Bread80/Datapoint2200/Decoder/Decoder.png

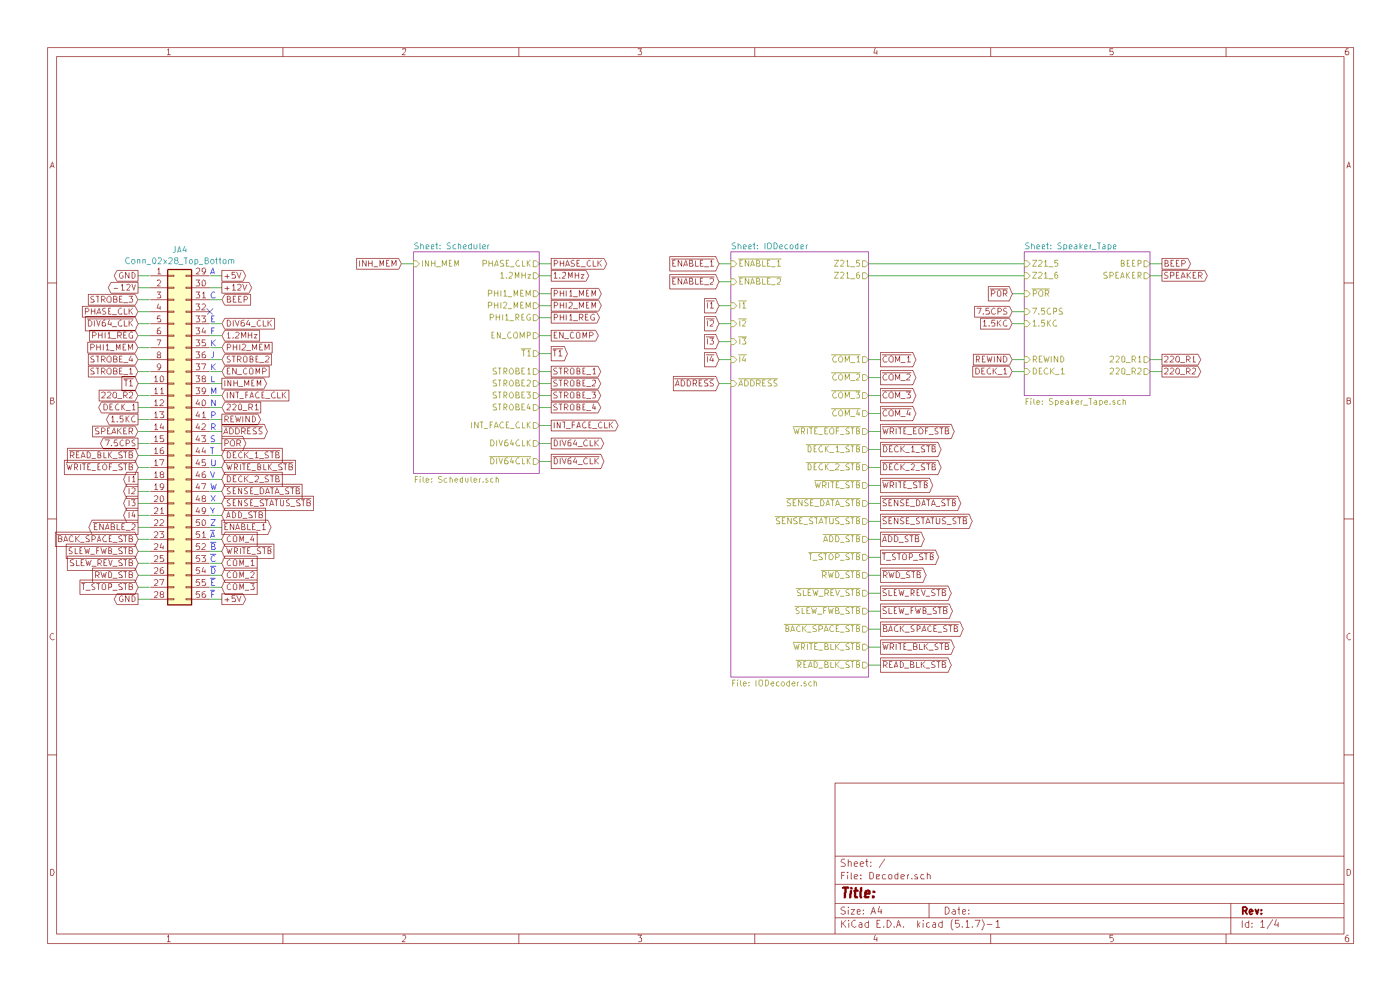
Decoder/Decoder.png
