Bread80/Datapoint2200/Decoder/IODecoder.png

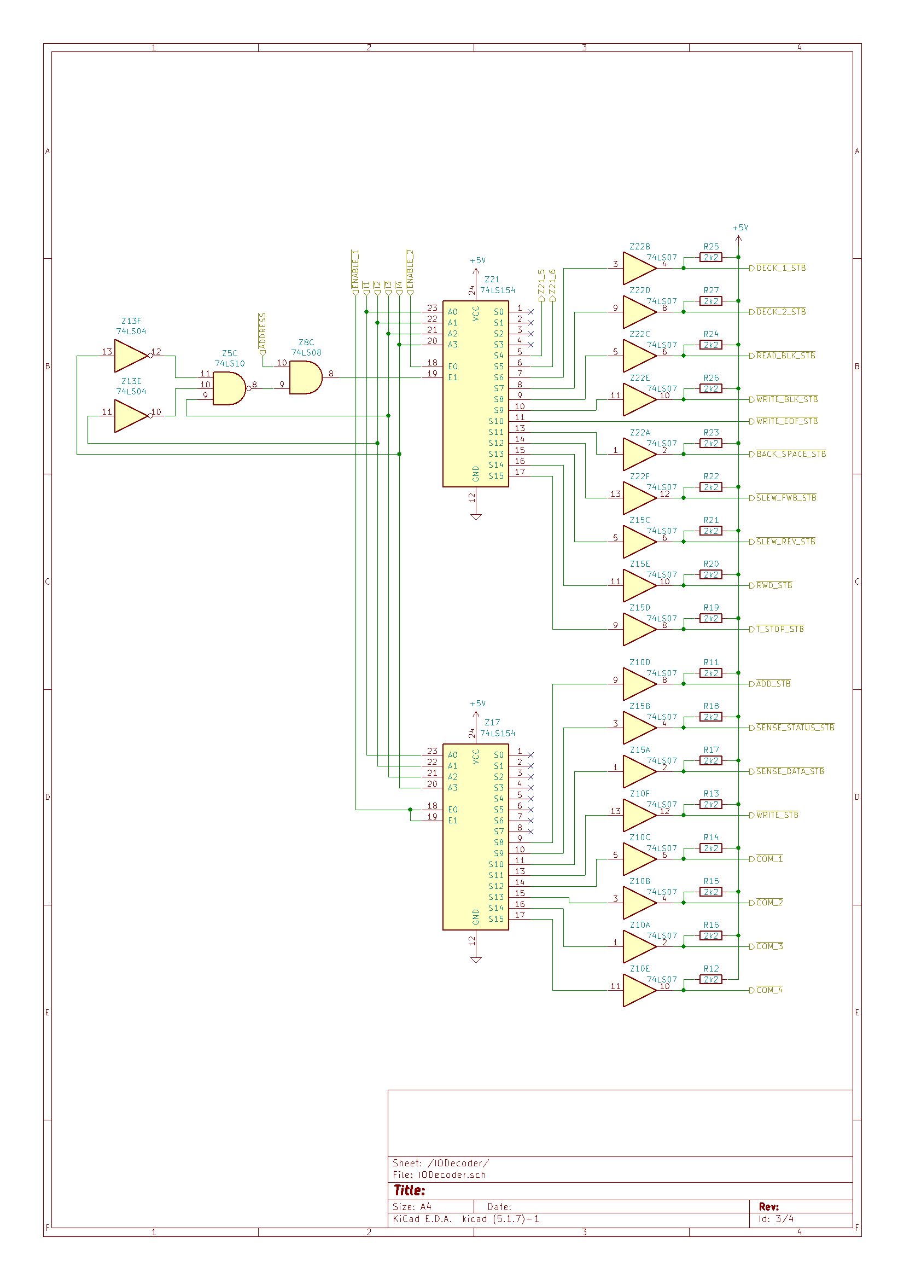
Decoder/IODecoder.png
