Bread80/Datapoint2200/Decoder/Scheduler.png

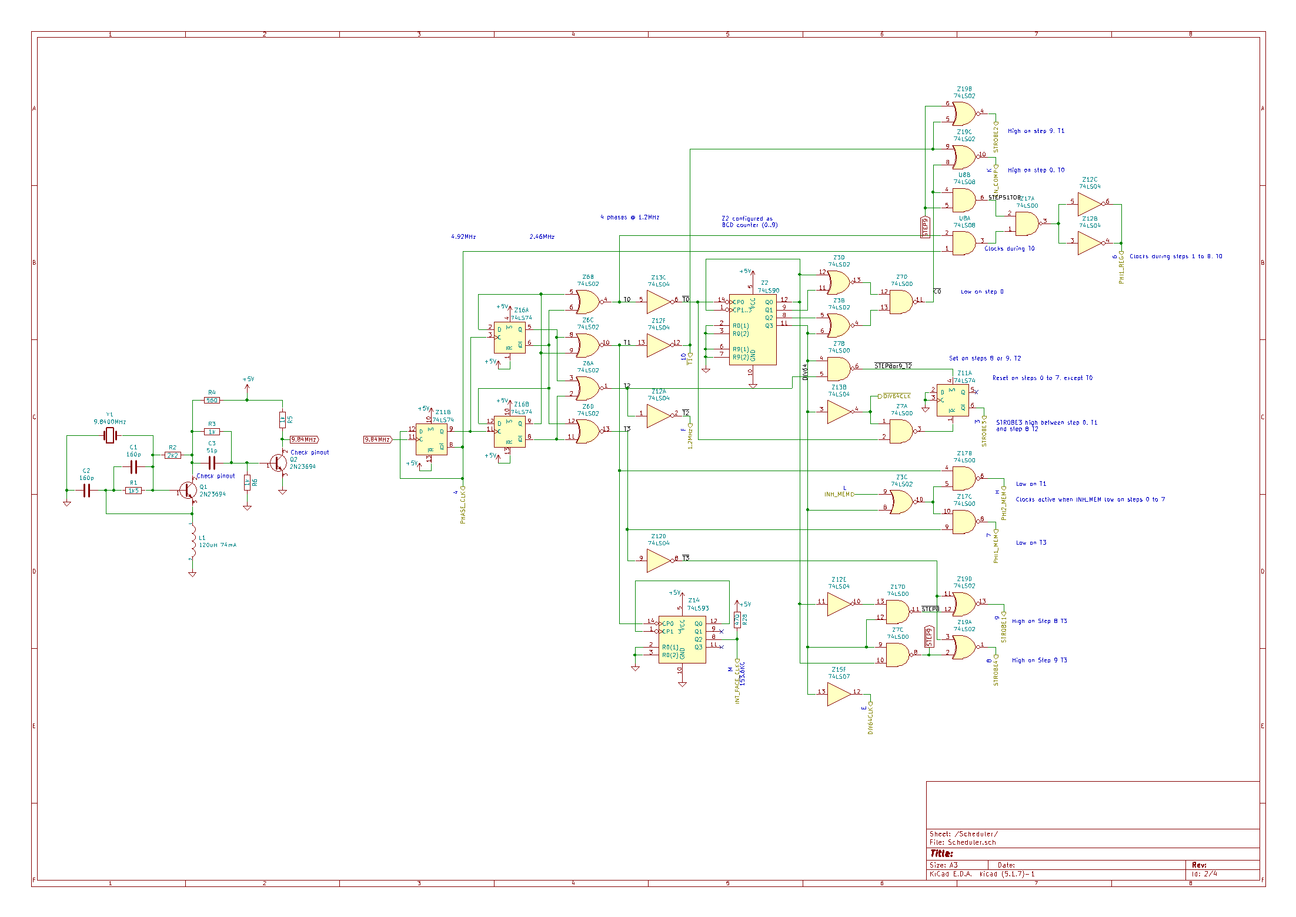
Decoder/Scheduler.png
