Bread80/Datapoint2200/Decoder/Speaker_Tape.png

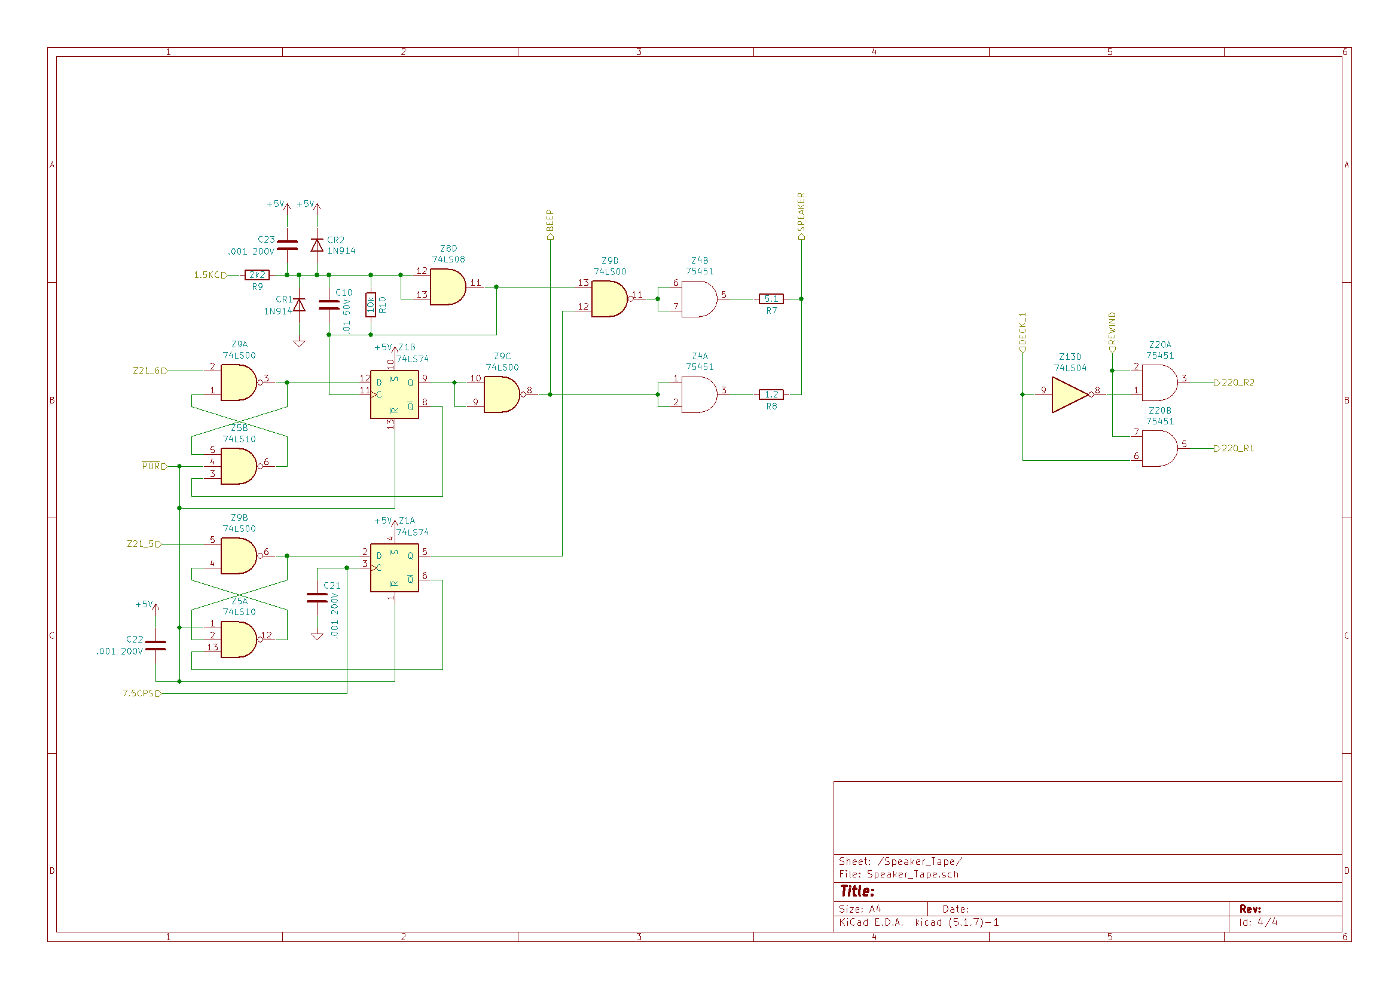
Decoder/Speaker_Tape.png
