Bread80/Datapoint2200/Processor/AddressReg.png

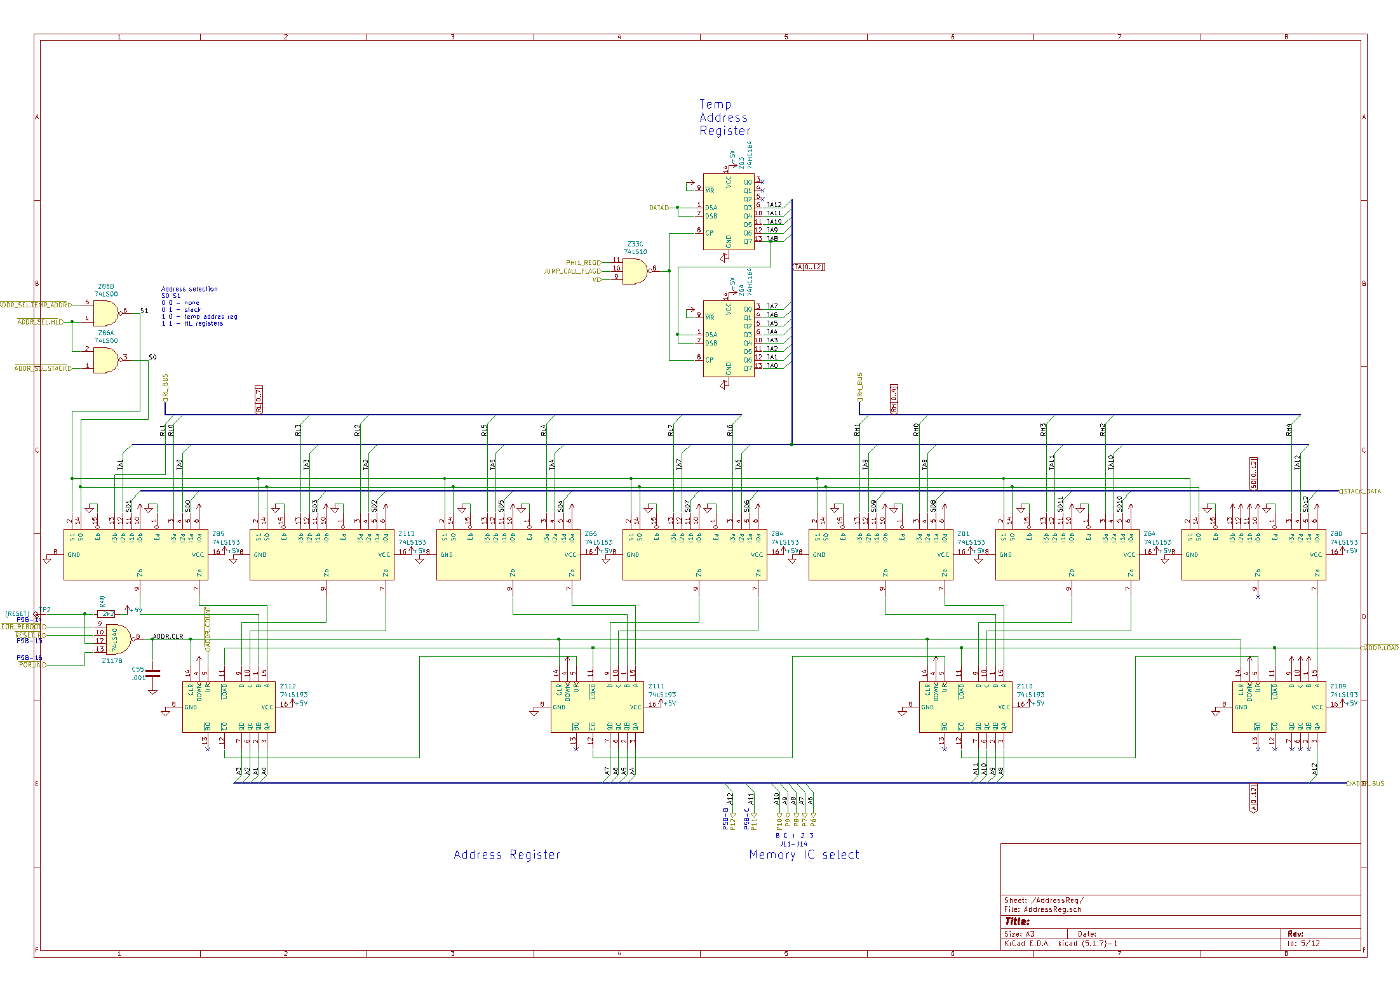
Processor/AddressReg.png
