Bread80/Datapoint2200/Processor/AddrRegAndStackControl.png

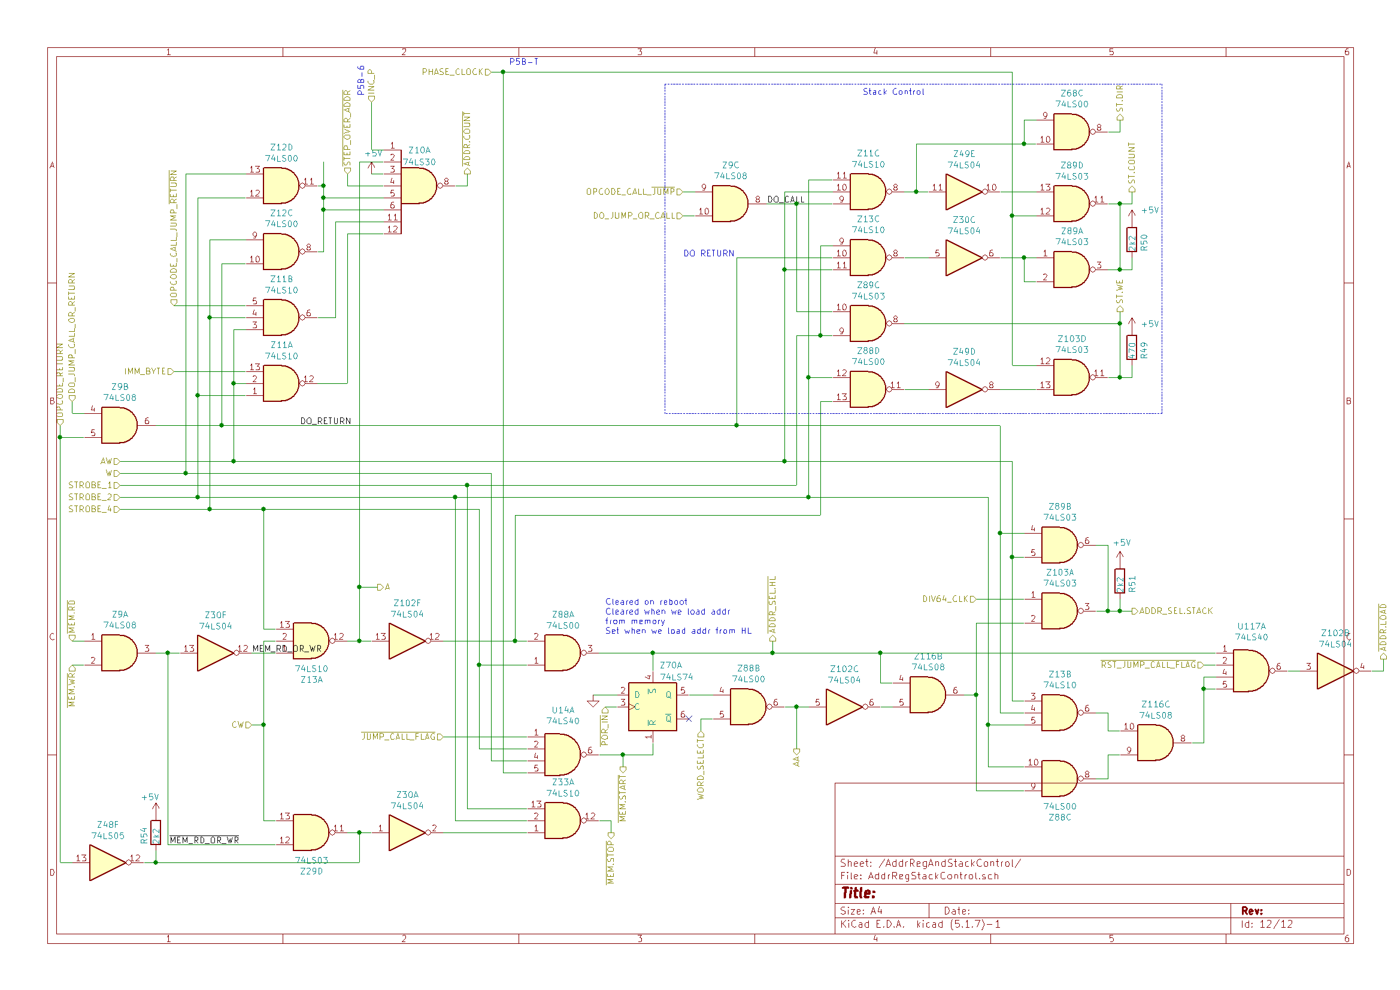
Processor/AddrRegAndStackControl.png
