Bread80/Datapoint2200/Processor/ARegister.png

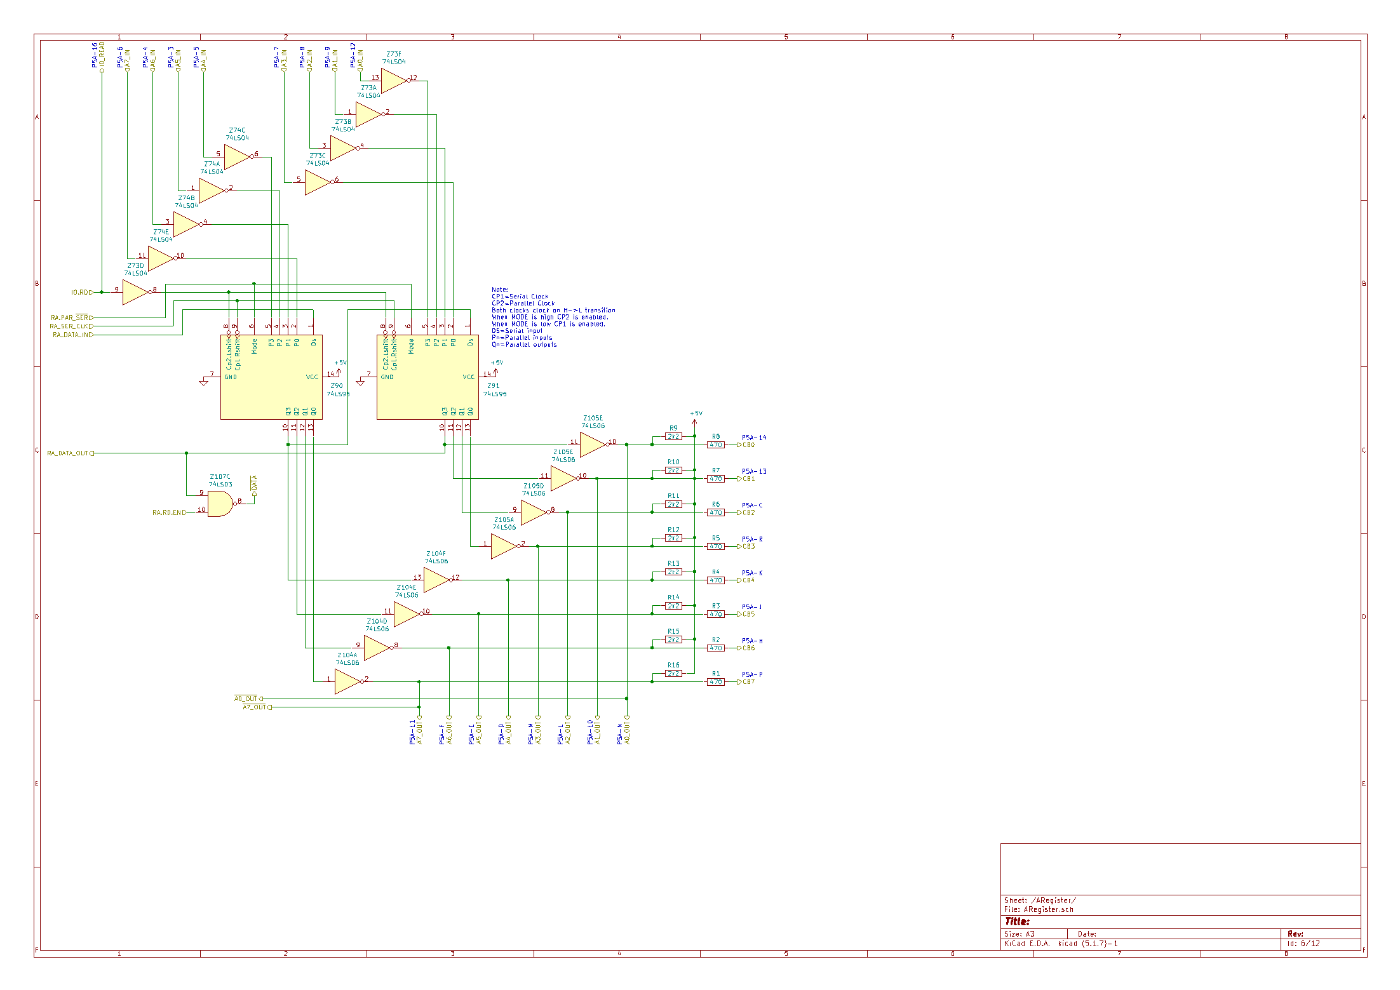
Processor/ARegister.png
