Bread80/Datapoint2200/Processor/Flags.png

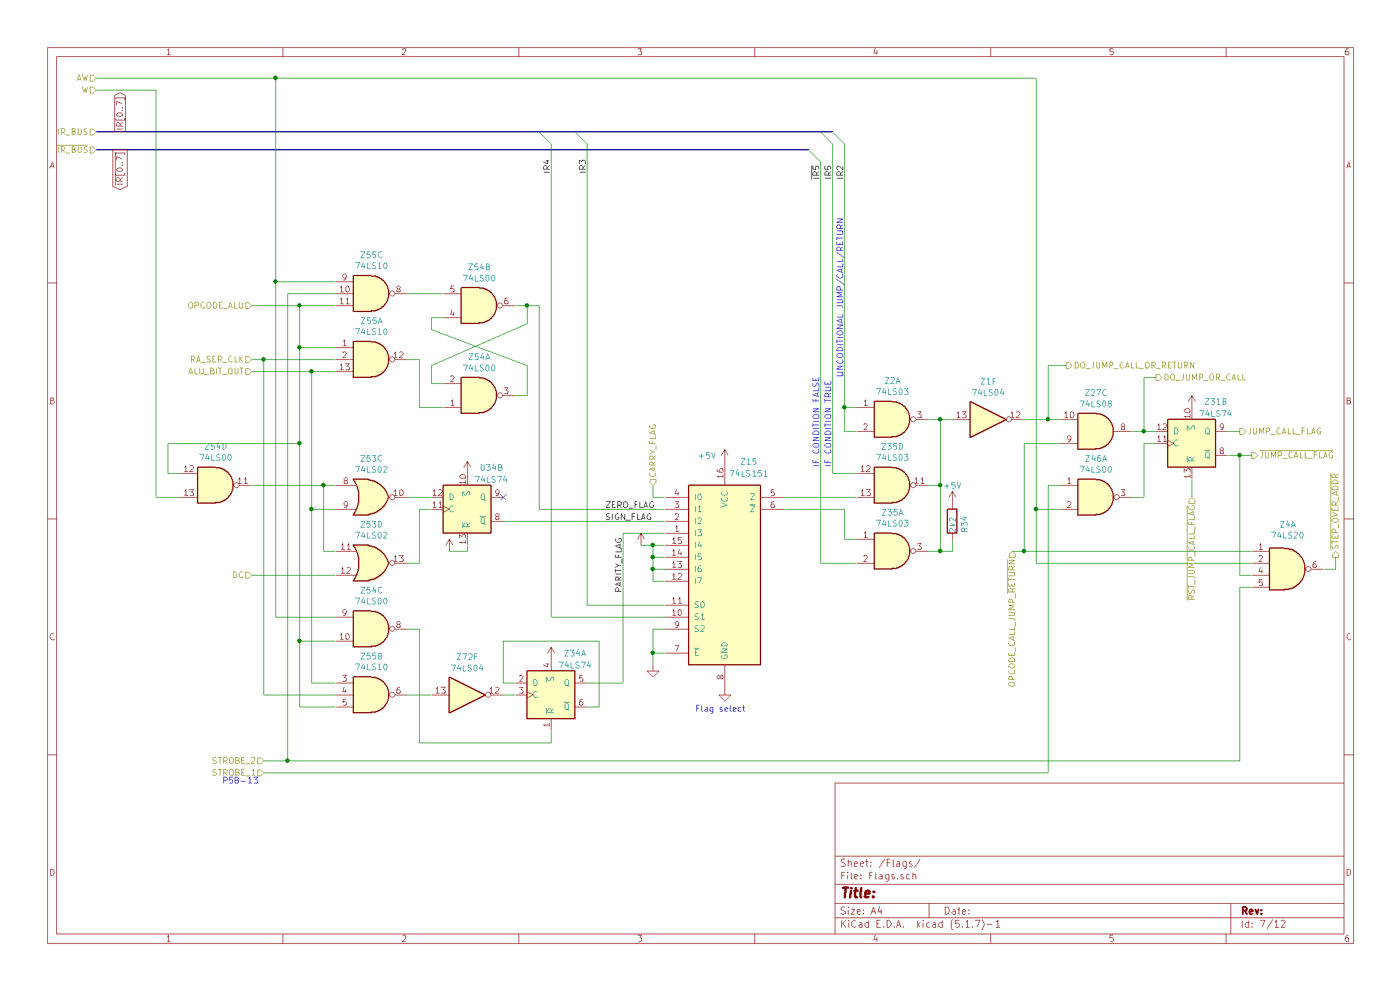
Processor/Flags.png
