Bread80/Datapoint2200/Processor/InstrDecoding.png

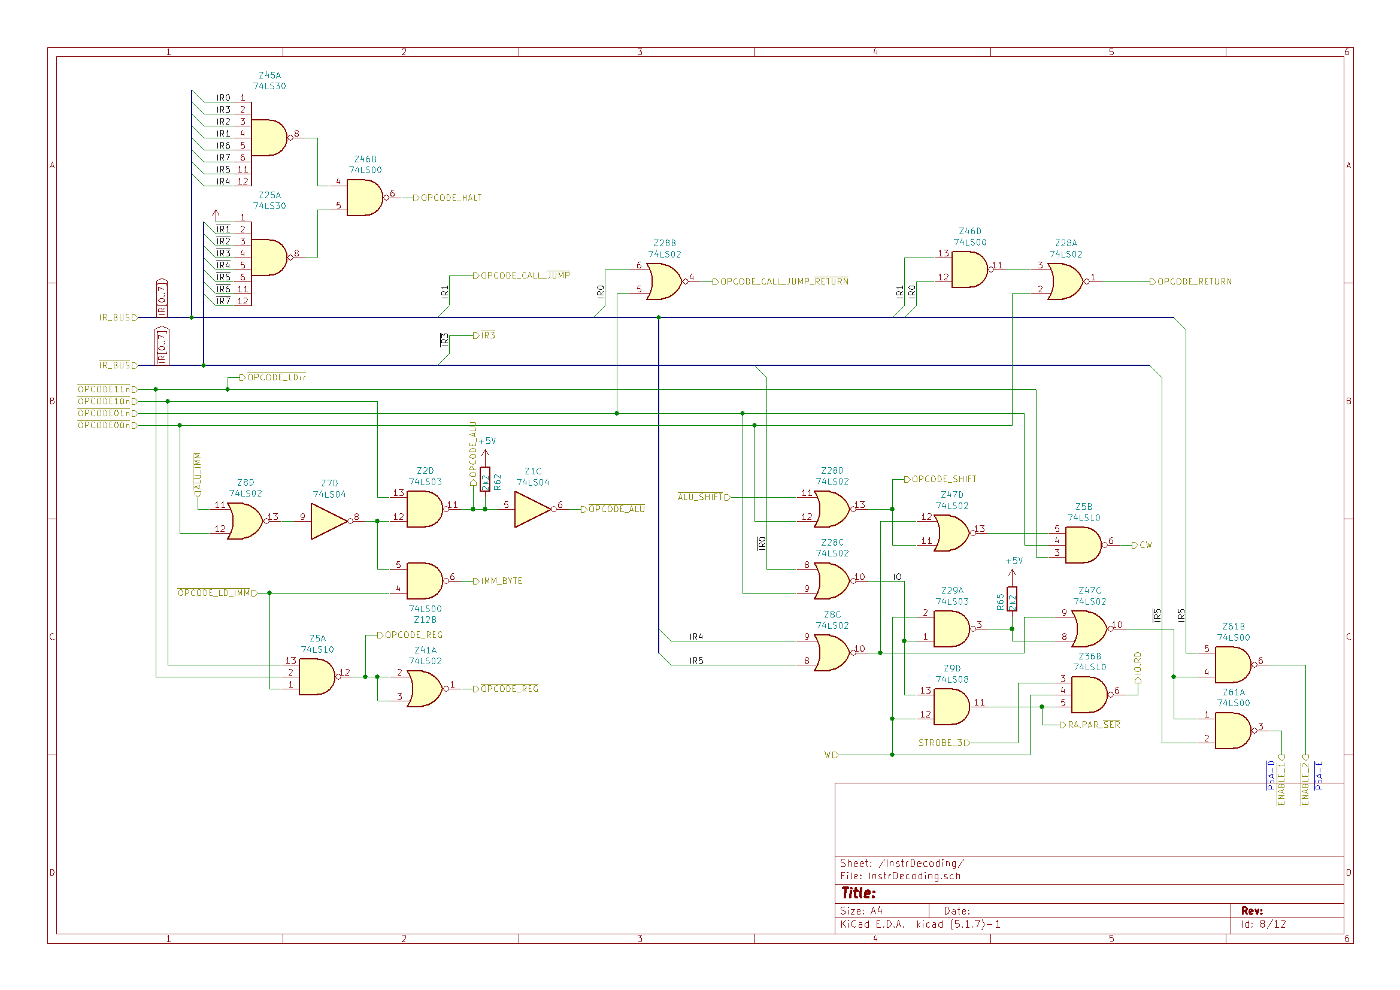
Processor/InstrDecoding.png
