Bread80/Datapoint2200/Processor/IRegister.png

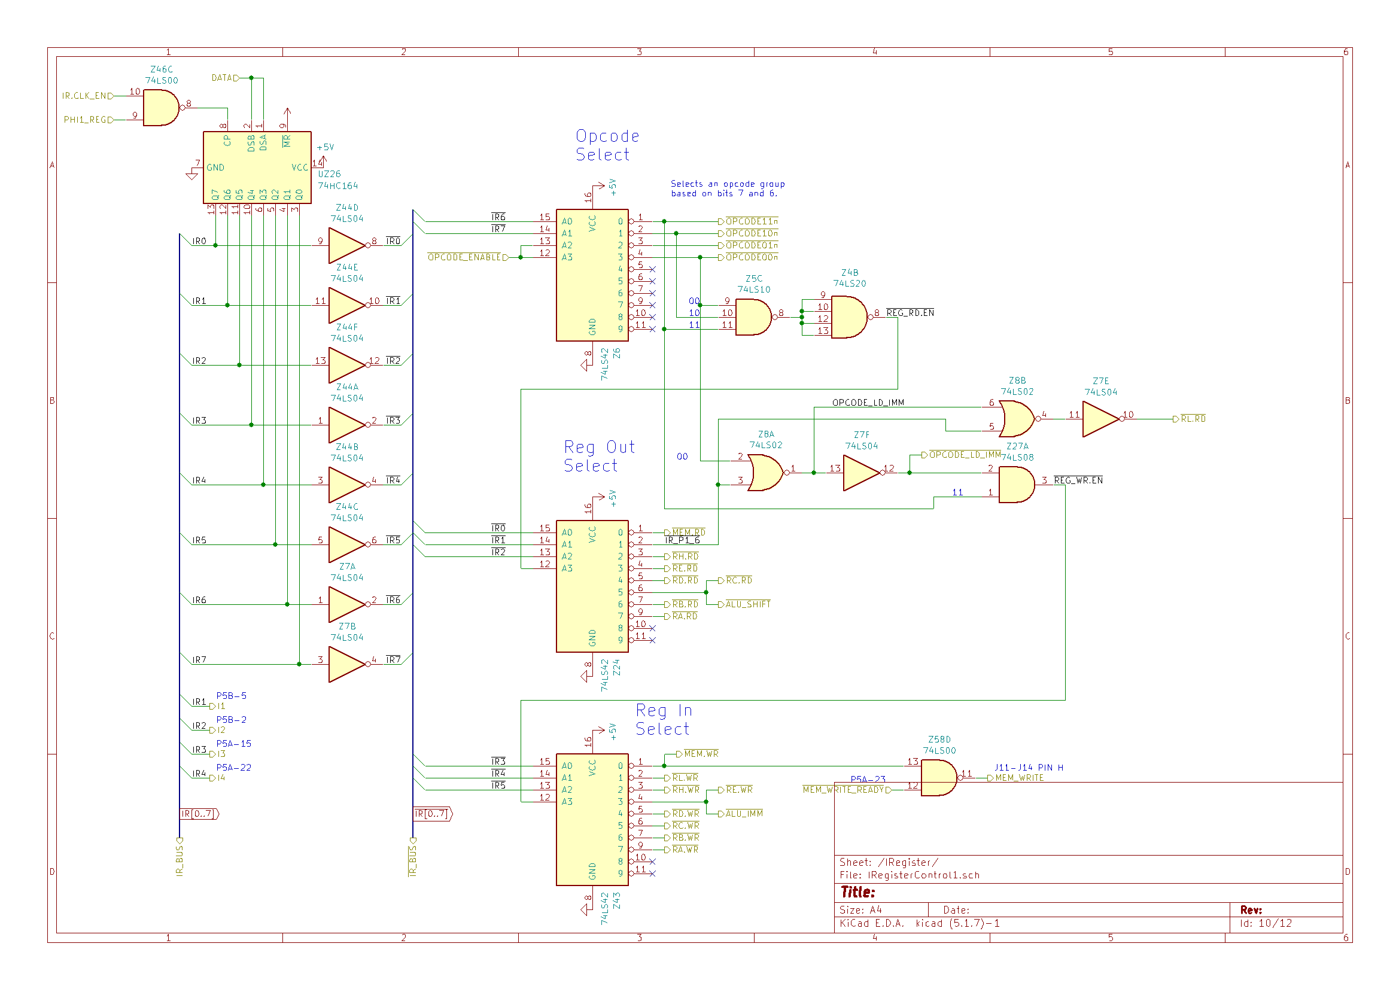
Processor/IRegister.png
