Bread80/Datapoint2200/Processor/Processor.png

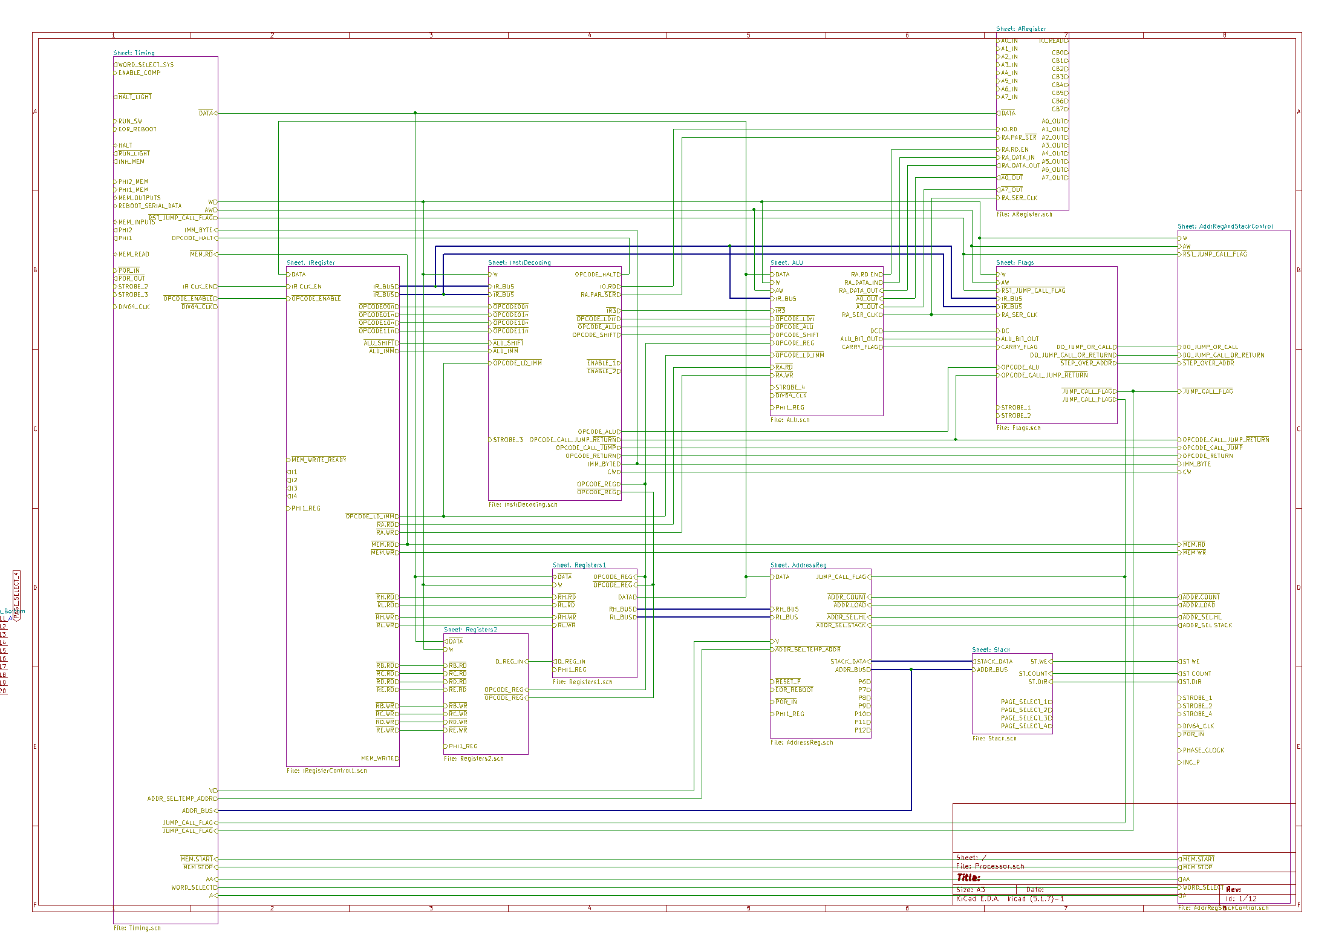
Processor/Processor.png
