Bread80/Datapoint2200/Processor/ProcessorRender.png

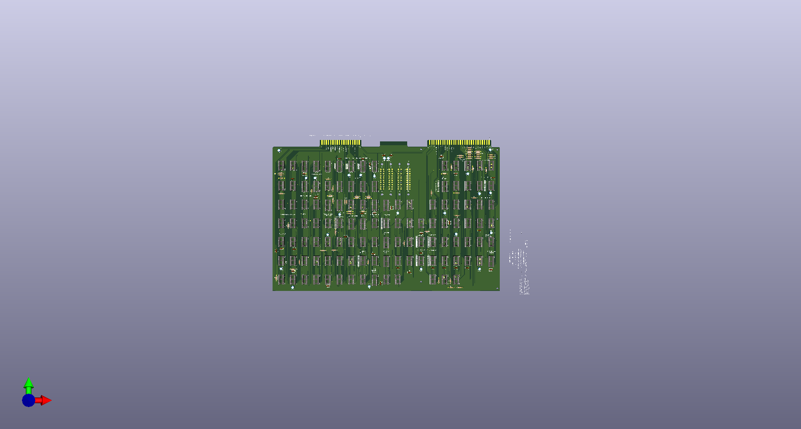
Processor/ProcessorRender.png
