Bread80/Datapoint2200/Processor/Registers2.png

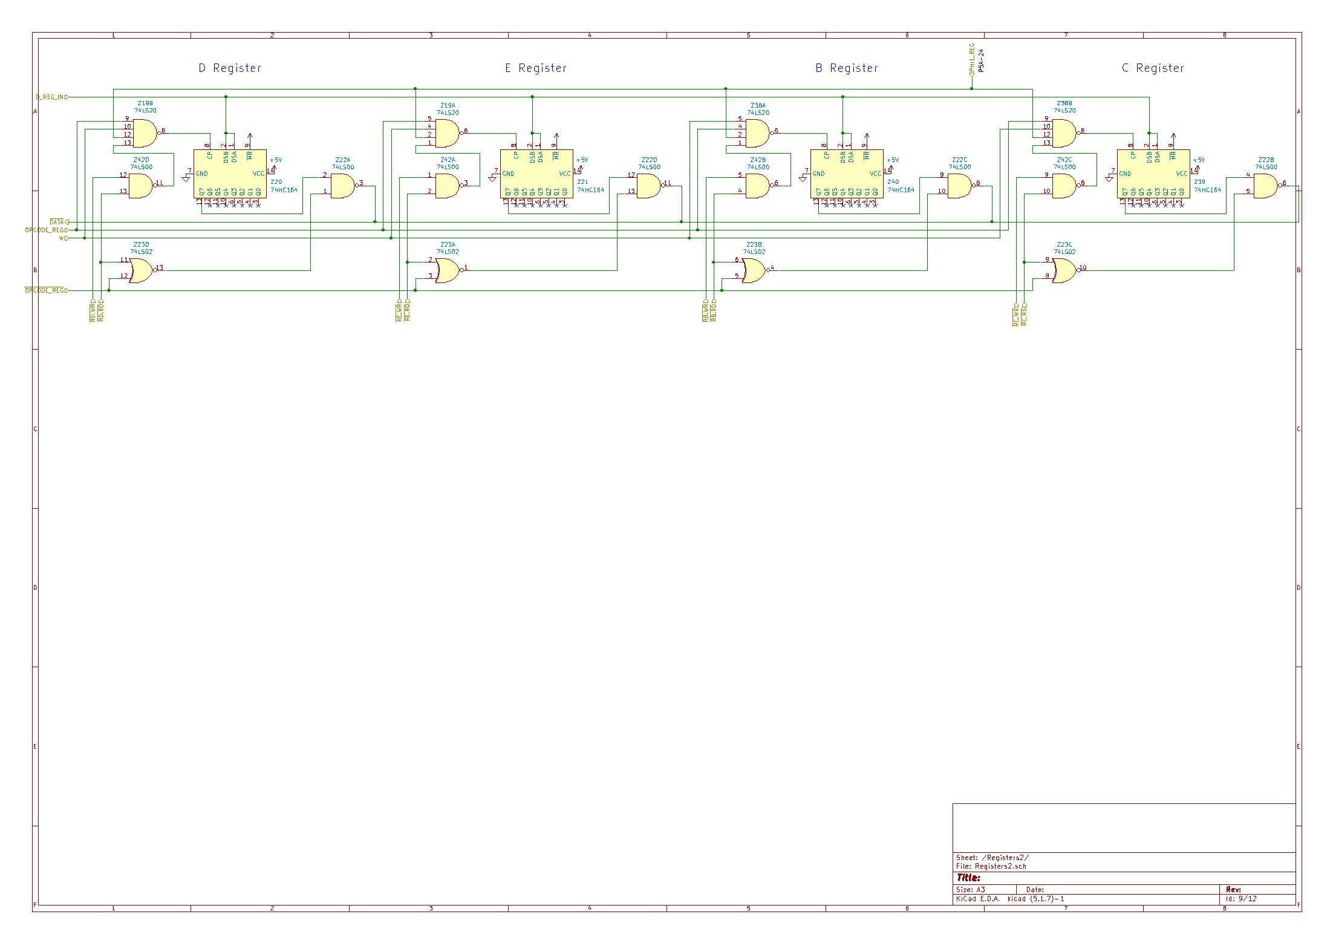
Processor/Registers2.png
