Bread80/Datapoint2200/Processor/Stack.png

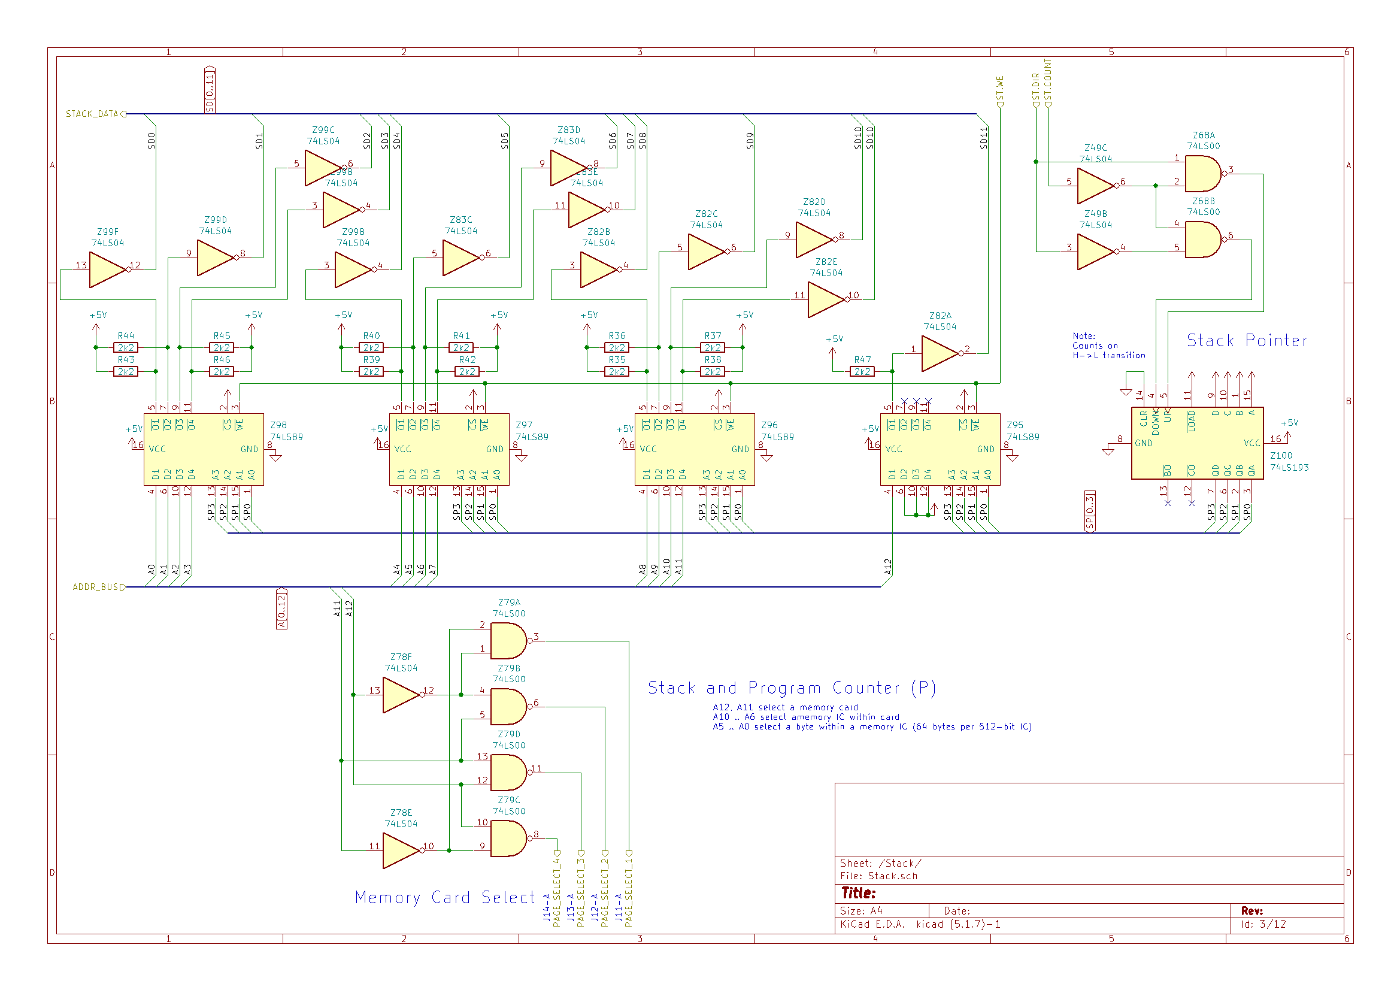
Processor/Stack.png
