Bread80/Datapoint2200/Processor/Timing.png

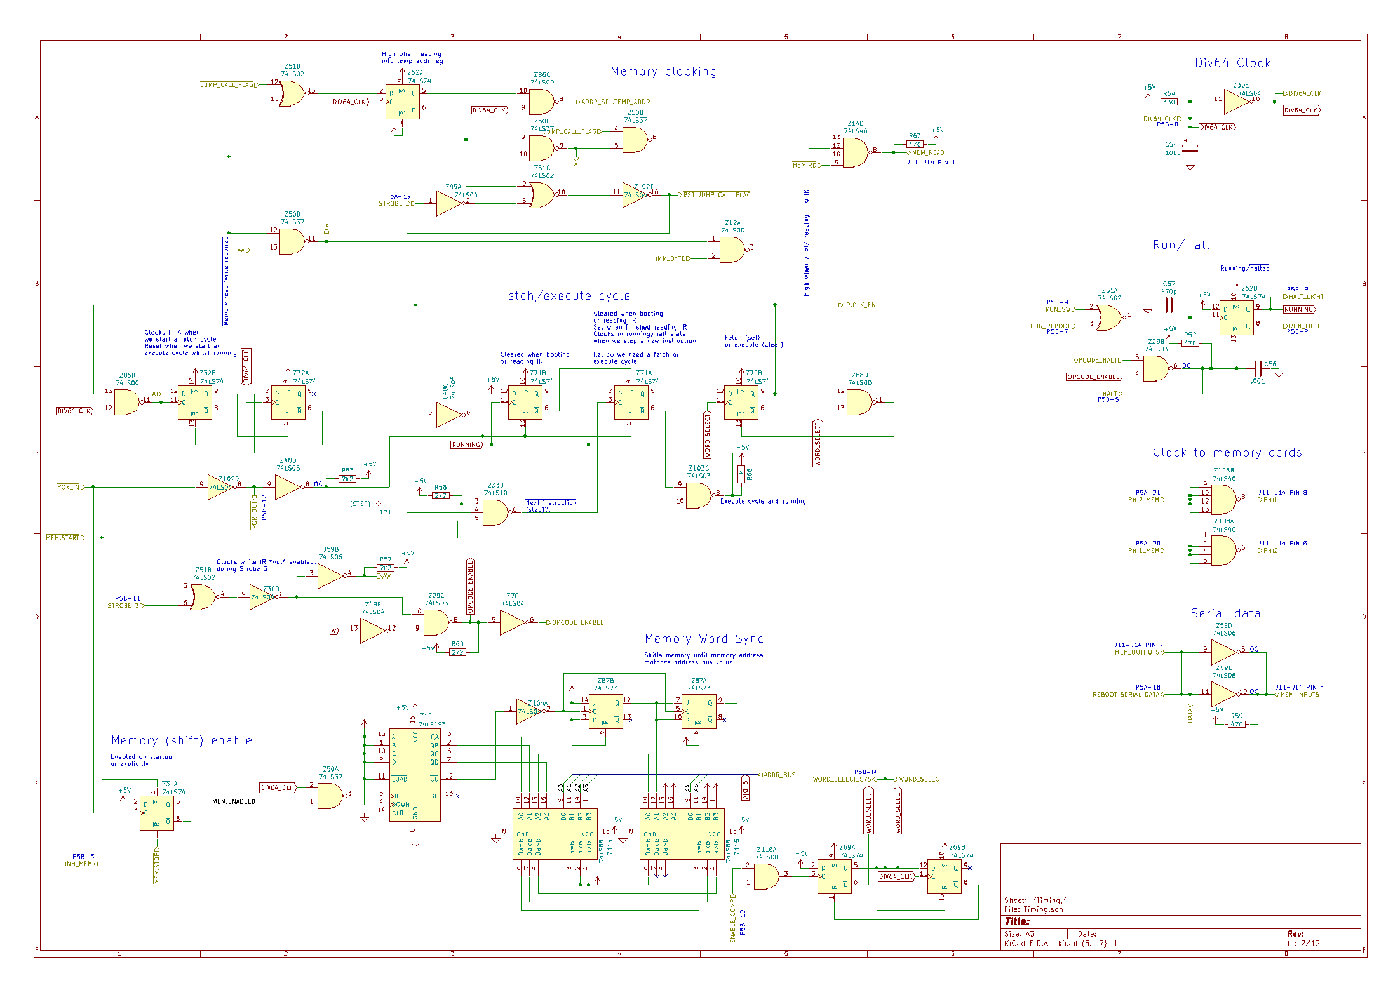
Processor/Timing.png
